JasonZ2030/CamProject/Images/IMG_0621.JPG

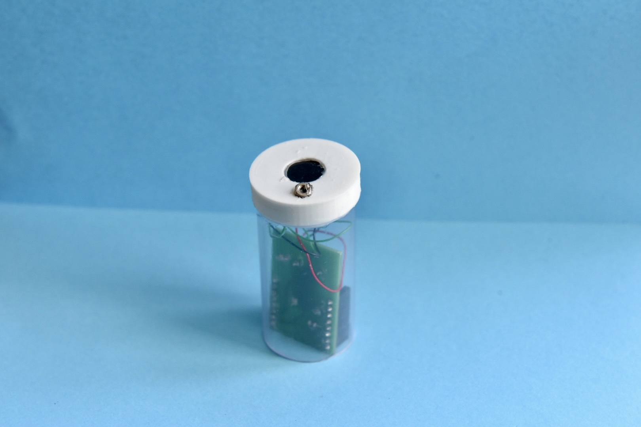
Images/IMG_0621.JPG
