JasonZ2030/CamProject/Images/IMG_0624.jpg

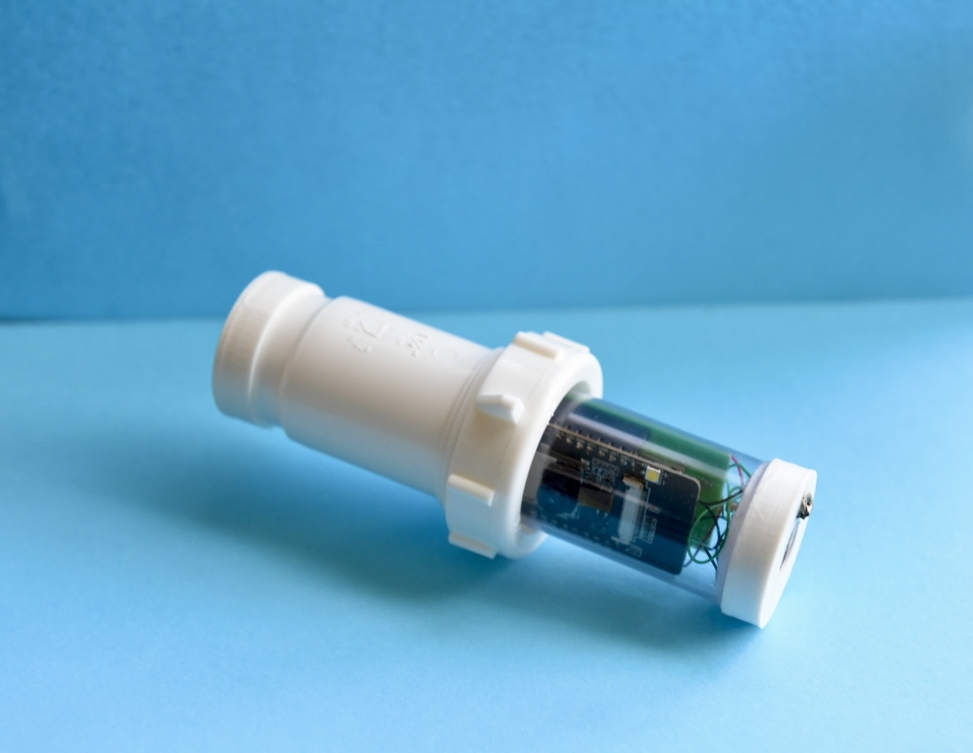
Images/IMG_0624.jpg
