JasonZ2030/CamProject/Images/IMG_0627.jpg

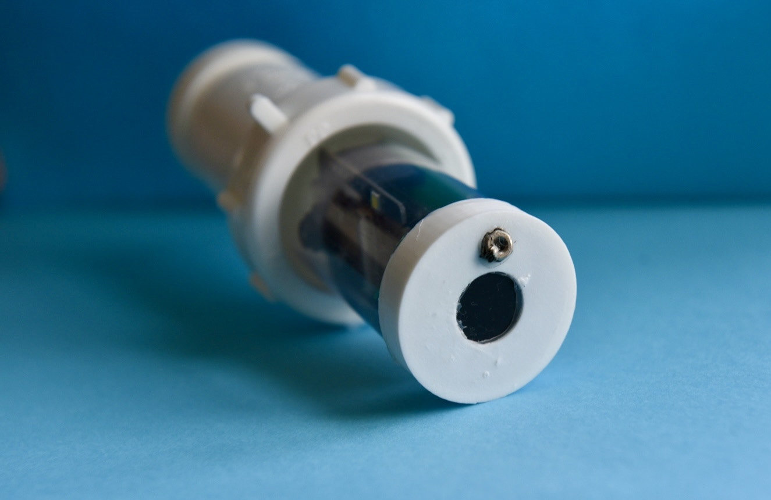
Images/IMG_0627.jpg
