JasonZ2030/CamProject/Images/IMG_0628.jpg

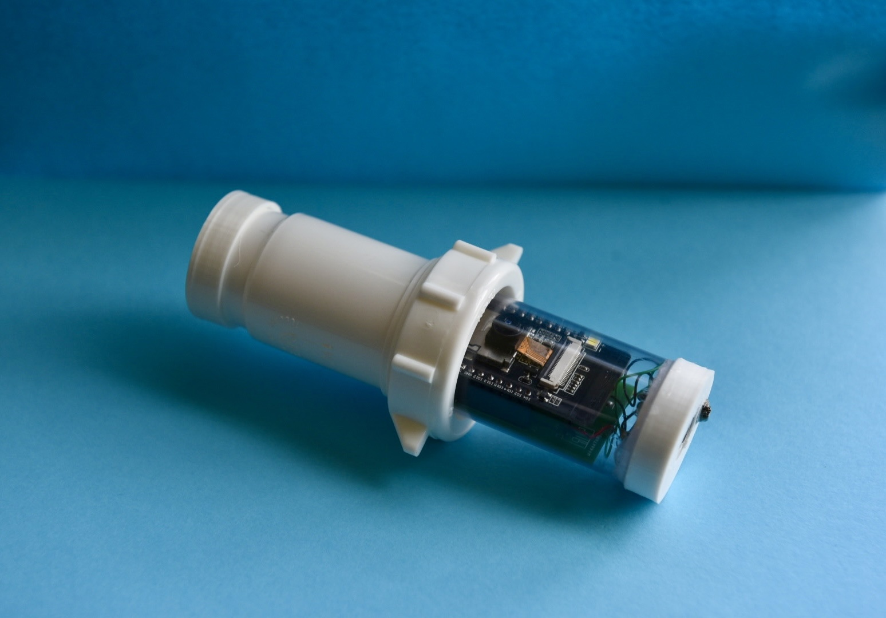
Images/IMG_0628.jpg
