JasonZ2030/CamProject/Images/IMG_0629.JPG

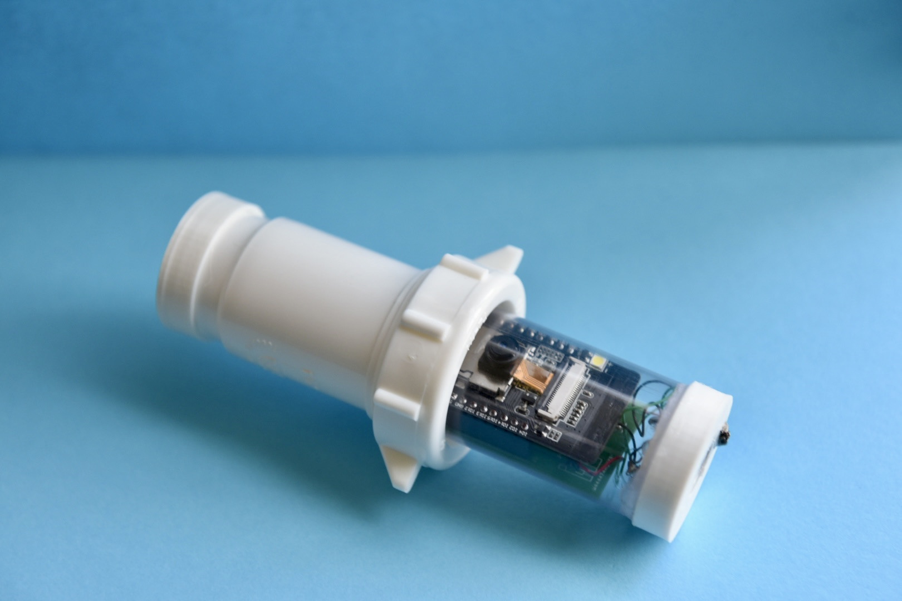
Images/IMG_0629.JPG
