JasonZ2030/CamProject/Images/IMG_0630.JPG

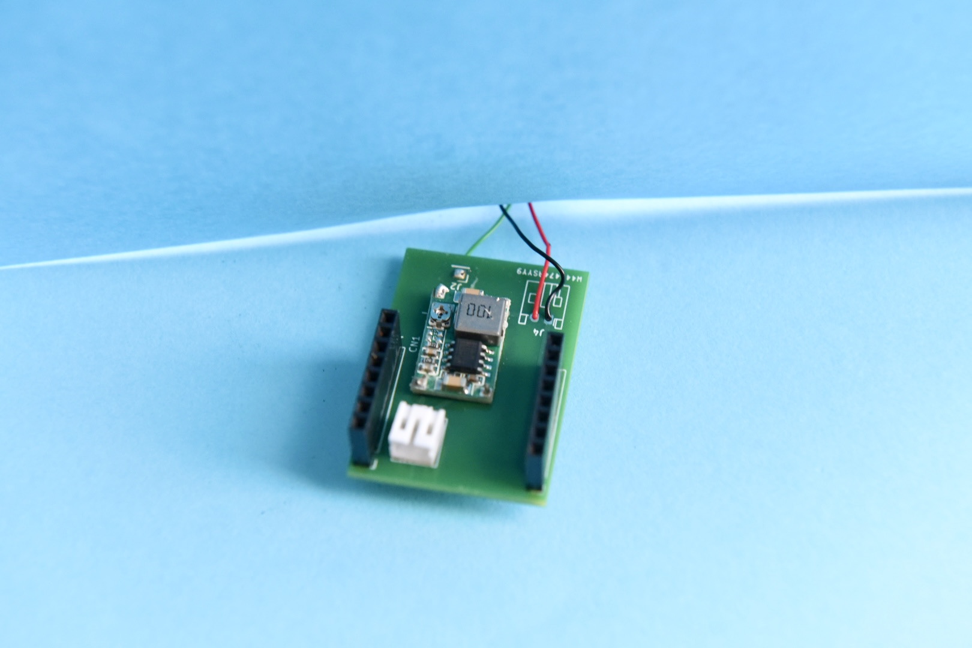
Images/IMG_0630.JPG
