JasonZ2030/CamProject/Images/IMG_0635.JPG

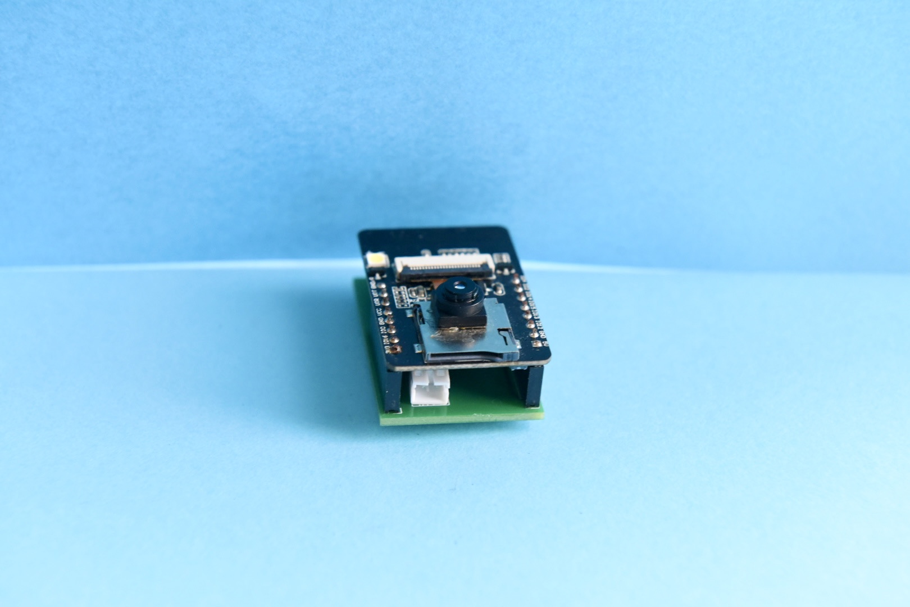
Images/IMG_0635.JPG
