JasonZ2030/CamProject/Images/IMG_0636.JPG

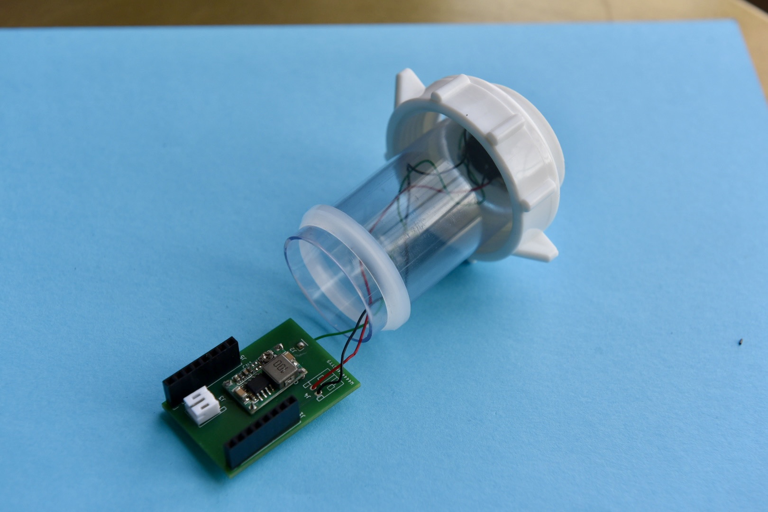
Images/IMG_0636.JPG
