JasonZ2030/CamProject/Images/IMG_0637.JPG

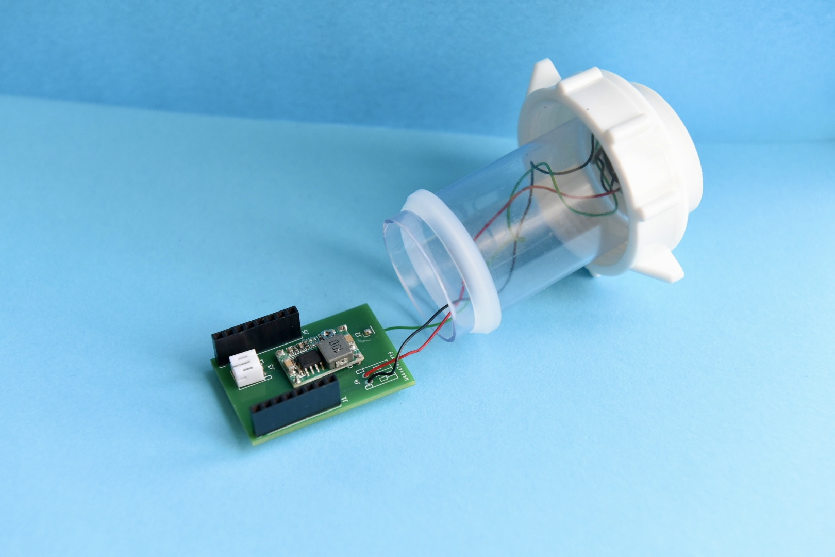
Images/IMG_0637.JPG
