JasonZ2030/CamProject/Images/IMG_0642.JPG

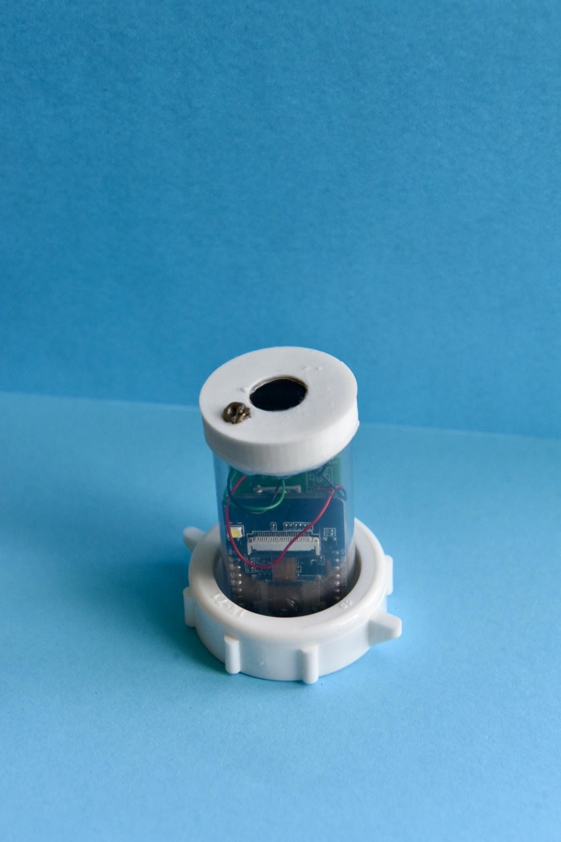
Images/IMG_0642.JPG
