JasonZ2030/CamProject/Images/IMG_0643.JPG

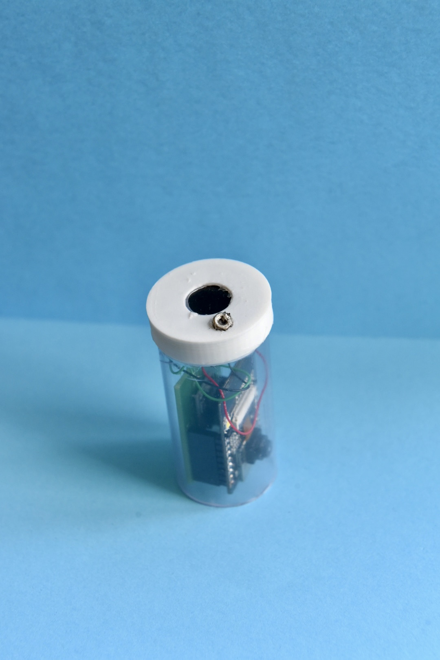
Images/IMG_0643.JPG
