JasonZ2030/CamProject/Images/Screenshot 2025-11-01 151332.png

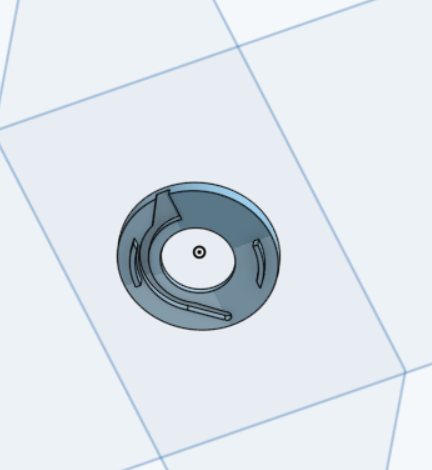
Images/Screenshot 2025-11-01 151332.png
